christoph-nils/DMX-Switch/Software/DMX-Switch/mydefs.h

/************************************************************************/
/*                                                                      */
/*                      Several helpful definitions                     */
/*                                                                      */
/*              Author: Peter Dannegger                                 */
/*                                                                      */
/************************************************************************/
#ifndef _mydefs_h_
#define _mydefs_h_
#include<avr/io.h>

//			Easier type writing:

typedef unsigned char  u8;
typedef   signed char  s8;
typedef unsigned short u16;
typedef   signed short s16;
typedef unsigned long  u32;
typedef   signed long  s32;

// Access bits like variables
struct bits {
	uint8_t b0:1, b1:1, b2:1, b3:1, b4:1, b5:1, b6:1, b7:1;
} __attribute__((__packed__));
#define SBIT_(port,pin) ((*(volatile struct bits*)&port).b##pin)
#define	SBIT(x,y)       SBIT_(x,y)


// avoid push in main
int main( void )        __attribute__((OS_main));


// force access of interrupt variables
#define IVAR(x)         (*(volatile typeof(x)*)&(x))

//			Optimization improvements


#define	OPTR18 __asm__ volatile (""::);		// it helps, but why ?
// remove useless R18/R19

// always inline function x
#define AIL(x)          static x __attribute__ ((always_inline)); static x

// never inline function x:

#define NIL(x)   x __attribute__ ((noinline)); x

// NOP
#define nop()           __asm__ volatile("nop"::)

// volatile access (reject unwanted removing access):

#define vu8(x)  (*(volatile u8*)&(x))
#define vs8(x)  (*(volatile s8*)&(x))
#define vu16(x) (*(volatile u16*)&(x))
#define vs16(x) (*(volatile s16*)&(x))
#define vu32(x) (*(volatile u32*)&(x))
#define vs32(x) (*(volatile s32*)&(x))

#define bit_is_set(sfr,bit) \
(_SFR_BYTE(sfr) & _BV(bit))

#endif
